XylenC4/ESP32CAM_QR-Code_MusicBox/ESP32-CAM_MusicBox/FastLED.ino

#define LED_PIN     12
#define NUM_LEDS    15
#define BRIGHTNESS  25
#define LED_TYPE    WS2811
#define COLOR_ORDER GRB

uint8_t iPalette = 0;
CRGB leds[NUM_LEDS];

#define UPDATES_PER_SECOND 100
uint16_t refresh_rate = UPDATES_PER_SECOND;

CRGBPalette16 currentPalette;
TBlendType    currentBlending;

extern CRGBPalette16 myRedWhiteBluePalette;
extern const TProgmemPalette16 RammsteinColors_p PROGMEM;
extern const TProgmemPalette16 Battery_Charging_p PROGMEM;
extern const TProgmemPalette16 Battery_Charged_p PROGMEM;
extern const TProgmemPalette16 Battery_Empty_p PROGMEM;


void setup_FastLED() {
  FastLED.addLeds<LED_TYPE, LED_PIN, COLOR_ORDER>(leds, NUM_LEDS).setCorrection( TypicalLEDStrip );
  fill_solid( currentPalette, 16, CRGB::White);
  FastLED.setBrightness( BRIGHTNESS );

  FastLEDColor(CRGB::White);

  currentPalette = RainbowColors_p;
  currentBlending = LINEARBLEND;
}

void loop_FastLED() {
  if (iPalette != 50) {
    static uint8_t startIndex = 0;
    startIndex = startIndex + 1; /* motion speed */

    FillLEDsFromPaletteColors(startIndex);

    FastLED.show();
    FastLED.delay(1000 / refresh_rate);

  } else {

    FastLED.setBrightness( 255 );
    FastLEDColor(CRGB::White);
    FastLED.show();
    delay(100);
    FastLEDColor(CRGB::Black);
    FastLED.show();
    delay(100);
    FastLEDColor(CRGB::Yellow);
    FastLED.show();
    delay(100);
    FastLEDColor(CRGB::Black);
    FastLED.show();
    delay(100);
    FastLEDColor(CRGB::Magenta);
    FastLED.show();
    delay(100);
  }
}

void FastLEDColor( const CRGB& rgb)
{
  for ( int i = 0; i < NUM_LEDS; i++) {
    leds[i] = rgb;
  }
  FastLED.show();
}

void FillLEDsFromPaletteColors( uint8_t colorIndex) {

  for ( int i = 0; i < NUM_LEDS; i++) {
    leds[i] = ColorFromPalette( currentPalette, colorIndex, 255, currentBlending);
    colorIndex += 3;
  }
}

void SelectPalette(int Palette) {
  iPalette = Palette;
  refresh_rate = UPDATES_PER_SECOND;
  
  FastLED.setBrightness( BRIGHTNESS );
  switch (Palette) {
    case 1:
      currentPalette = CloudColors_p;
      currentBlending = LINEARBLEND;
      break;
    case 2:
      currentPalette = LavaColors_p;
      currentBlending = NOBLEND;
      break;
    case 3:
      currentPalette = OceanColors_p;
      currentBlending = LINEARBLEND;
      break;
    case 4:
      currentPalette = ForestColors_p;
      currentBlending = NOBLEND;
      break;
    case 5:
      currentPalette = RainbowColors_p;
      currentBlending = LINEARBLEND;
      break;
    case 6:
      currentPalette = RainbowStripeColors_p;
      currentBlending = NOBLEND;
      break;
    case 7:
      currentPalette = HeatColors_p;
      currentBlending = LINEARBLEND;
      break;
    case 8:
      currentPalette = LavaColors_p;
      currentBlending = LINEARBLEND;
      break;
    case 9:
      currentPalette = RainbowStripeColors_p;
      currentBlending = LINEARBLEND;
      break;
    case 10:
      currentPalette = ForestColors_p;
      currentBlending = LINEARBLEND;
      break;
    case 50:
      break;
    case 80:
      currentPalette = RammsteinColors_p;
      currentBlending = NOBLEND;
      break;
    default:
      currentPalette = RainbowColors_p;
      currentBlending = LINEARBLEND;
      break;
  }
}

void SelectChargingPalette(int State) {
  switch (State) {
    case 1:
      currentPalette = Battery_Charged_p;
      currentBlending = NOBLEND;
      break;
    case 2:
      currentPalette = Battery_Charging_p;
      currentBlending = NOBLEND;
      break;
    case 3:
      currentPalette = Battery_Empty_p;
      currentBlending = NOBLEND;
      break;
    default:
      break;
  }
}

const TProgmemPalette16 RammsteinColors_p PROGMEM =
{
  CRGB::Black,
  CRGB::White,
  CRGB::White,
  CRGB::Black,
  CRGB::Black,
  CRGB::White,
  CRGB::White,
  CRGB::Black,
  CRGB::Black,
  CRGB::White,
  CRGB::White,
  CRGB::Black,
  CRGB::Black,
  CRGB::White,
  CRGB::White,
  CRGB::Black
};

const TProgmemPalette16 Battery_Charging_p PROGMEM =
{
  CRGB::Yellow,
  CRGB::White,
  CRGB::Yellow,
  CRGB::White,
  CRGB::Yellow,
  CRGB::White,
  CRGB::Yellow,
  CRGB::White,
  CRGB::Yellow,
  CRGB::White,
  CRGB::Yellow,
  CRGB::White,
  CRGB::Yellow,
  CRGB::White,
  CRGB::Yellow,
  CRGB::White
};

const TProgmemPalette16 Battery_Charged_p PROGMEM =
{
  CRGB::Yellow,
  CRGB::White,
  CRGB::Yellow,
  CRGB::White,
  CRGB::Yellow,
  CRGB::White,
  CRGB::Yellow,
  CRGB::White,
  CRGB::Yellow,
  CRGB::White,
  CRGB::Yellow,
  CRGB::White,
  CRGB::Yellow,
  CRGB::White,
  CRGB::Yellow,
  CRGB::White
};


const TProgmemPalette16 Battery_Empty_p PROGMEM =
{
  CRGB::Red,
  CRGB::White,
  CRGB::Red,
  CRGB::White,
  CRGB::Red,
  CRGB::White,
  CRGB::Red,
  CRGB::White,
  CRGB::Red,
  CRGB::White,
  CRGB::Red,
  CRGB::White,
  CRGB::Red,
  CRGB::White,
  CRGB::Red,
  CRGB::White
};
